taeseokyi/reefkeeper/docs/notes/feedback-one-change-at-a-time.md

# feedback-one-change-at-a-time

> KH 측정 시스템 튜닝/실험은 한 번에 하나씩만 변경하고 효과 측정 후 다음으로

---

아쿠아위즈 KH 측정 시스템의 파라미터·시퀀스 튜닝 시 **한 번에 한 가지만 변경**하고 그 ΔpH/dKH 효과를 측정한 뒤 다음 변경으로 넘어간다. 여러 개를 동시에 바꾸면 어느 요인이 작용했는지 규명 불가.

**Why:** 폭기 30→20분과 대칭화(ref/tank 분리측정)를 동시 적용해 "30 vs 20" 비교가 교란된 전례가 있음 ([project-kh-offset-aeration-test](project-kh-offset-aeration-test.md)).

**How to apply:** 변경 후보가 여러 개여도(폭기시간·헹굼제거·`STABLE_SECS`·`CONV_EPS` 등) 묶지 말고 순차 적용, 각 단계마다 정시 측정(05:00/13:00/21:00)으로 효과를 확인한 뒤 다음으로. 변경 전에는 현 상태를 먼저 관찰(예: 21:00 ΔpH 변동)해 기준선을 잡는다.

**단위는 "변수 개수"가 아니라 "인과 축(메커니즘)" (사용자 정정 2026-06-16):** `STABLE_SECS`(샘플링 전 안정화)와 `CONV_EPS`(수렴 채택문턱)는 **둘 다 "안착·평형된 값만 채택"하는 동일 축**이라 한 묶음으로 동시 변경해도 원칙 위배 아님(같은 가설 검정). 분리 기준은 서로 다른 메커니즘일 때 — 폭기/CO₂(`ron`·`AIR_SECS`) vs 경로/접합(헹굼·KCl) vs 안정성(STABLE·CONV_EPS). **같은 축의 2변수를 "분리 안 됨"이라 경고하지 말 것(과한 경고).**
