taeseokyi/reefkeeper/docs/notes/project-kh-v4-firmware-state.md

# project-kh-v4-firmware-state

> "KH 측정 현재 상태 스냅샷(2026-06-17 말) — V4 평형추종 측정 + 신펌웨어(트림평균) 플래시 완료, dkh.dat 규약, 미해결 핵심=폭기가스 안정화"

---

이번 세션(2026-06-17) 끝 시점의 **현재 상태 + 다음 단계** 스냅샷. 상세 이력은 [project-kh-offset-aeration-test](project-kh-offset-aeration-test.md)와 `docs/measurement-ledger.md`(측정 시각순+코드버전 V0~V4 정의+진단).

**측정 코드 = V4 (`bin/measure_kh_once.py`, Windows `C:\dkh\work`에도 배포):**
- **폭기 중 측정 + 진짜 평형(평탄)까지.** 평탄 판정 = **정수 milli-pH 윈도우 span**: 최근 4개 `round(ph*1000)`의 max−min ≤ **2 mpH**. (float 비교 `abs(d)<=0.001`은 0.001 경계 지터로 못 씀 → 정수 비교. 연속-Δ는 느린 크리프에 조기 latch라 폐기.)
- 2-phase: **[A]** tank·ref 동시폭기 + tank 평탄까지 측정(ref는 홀딩서 co-aeration) → **전이 무대기**(airoff → `m1b:82` 완전배출[오염방지, 단축불가] → `m2f:60`) → **[B]** ref 평탄까지(co-aeration이라 빨리). 간격 30s.
- **무한대기 방지:** `PHASE_MAX_SECS=2400`/phase + `MEAS_MAX=80` + 연속 측정실패 `FAIL_MAX=5` + 시리얼 read 타임아웃. 미평탄 상한 도달 시 마지막값+경고(행 안 함).
- 오류/비정상 종료 시 `_safe_cleanup`(에어OFF+측정챔버 배출+KCl 소크 복원). KCl 소크 완료 미검증이면 에러로 0.0 기록.

**dkh.dat 규약** (`HH ref_pH tank_pH ref_kh(8.448) tank_kh temp`):
- **에러 표식 = 5값 전부 0**(측정실패/타임아웃/KCl소크 실패). ★**에러 래치**: 측정 전 마지막 줄이 에러표식이면 *측정 생략하고 에러표식만 재기록* — 수동으로 마지막 에러줄 삭제 전까지(오류 무인 반복 방지).
- **평탄 미도달 = `tank_kh` 음수(−)** 표식(값 크기 유지). 전부-0 에러표식과 구분돼 래치 안 걸림.
- 서버 `bin/dkh_server.py`는 `float(parts[4])` 그대로 반환 → **음수 그대로 출력**(수정 불요). 0.0=에러.

**진단 도구:** `bin/test_aeration_plateau.py`(tank 단일 평형곡선; V4와 **동일 평탄기준**, 종료 시 finally서 KCl 소크). `bin/plateau_analyze.py`(CSV 오프라인 알고리즘 검증).

**펌웨어 (2026-06-17 ~20:50 플래시·`help` 검증 완료, 보드 라이브):**
- **전위 = 트림 평균**(`TRIM_N=16`: 64샘플 정렬 후 상·하위 16개 버리고 중앙 32개 평균; 버블 스파이크 제거). 차동이라 절대 pH만 미세변동, dKH 무영향.
- **seq / air: / wait: 명령 제거**(미사용·레거시) → flash 98→90%, RAM 83→58%.
- **신규 명령: `roff`/`toff`**(D12 에어/D13 PWM 선택 OFF; ron/ton의 짝), **`stop`**(전체 모터+핀 OFF=motorAllStop+stopAir). help/status 정리(status에 D12/D13 핀상태 표시).
- 플래시 방법: 클론 Nano(CH341)=신 부트로더(`arduino:avr:nano`). **HC-06이 D0/D1 하드웨어 시리얼 공유**라 보드에 꽂은 채론 USB 업로드 충돌→**Nano 빼서 단독 USB 플래시**. 단독 시 ADS1115 없어 `while(1)` 정지(ino) → help 검증은 보드 재장착 후 COM15(블루투스)로.

**★★★밀폐 검증 ①② 모두 성공 = 밀폐 우위 확정 (2026-06-19 05:00+13:00):**
- 밀폐 두 점: `05 7.976 7.968 …8.283 28.1`(ΔpH −0.008) / `13 7.957 7.947 …8.255 28.6`(ΔpH −0.010). 둘 다 tank 4회·125s/ref 6회·203s 평탄(span≤2), 단조·진짜 평탄·경고 없음·빠름.
- **검증① (새벽 dip 소멸) 성공:** 3회 재현되던 −0.043~−0.059 dip이 **−0.008**로 붕괴 = 방 CO₂ 유입 차단. 절대pH ~7.97로 6/17 새벽(7.97, −0.058)과 같은 수준인데 dip만 소멸=깨끗한 대조.
- **검증② (증발 흩어짐↓) 성공:** 새벽→낮 dKH 점프가 **개방 +0.29(6/18 7.657→7.950) → 밀폐 −0.03(8.283→8.255)로 ~10배 축소.** 6/18 +0.29를 만들던 한낮 증발 농축이 밀폐로 사라짐. 두 밀폐 점 타이트 군집(ΔpH −0.008/−0.010, dKH 8.283/8.255). 절대pH도 ~7.97→7.95 거의 불변(개방 0.4 스윙 대비)=헤드스페이스가 5L 버퍼로 핀고정→방CO₂ 일주기서 분리. 공통모드 ~20mpH 동시하강에도 ΔpH 보존=차동 정확.
- **부수효과 = 평탄 폭발적 단축(드리프트 레버 a+b 동시):** 과거 새벽 33회→4회, ~50분→~5분 → tank↔ref gap 붕괴 → 17:08식 inter-phase 드리프트 구조 제거. 28.6℃까지 펌프발열 폭주 없음.
- **원시오차 −0.78→~−0.18(−0.165/−0.193), 영점보정 필요성 약화·급하지 않음:** 무보정으로 이미 ±0.25 안. offset이 작고 안정해 보이나 **n=2·동일물/전극 → 21:00·시계열(또는 신선해수 새 널)로 재확인 후 영점보정 결정**([feedback-validation-independent-replication](feedback-validation-independent-replication.md)).
- **★★★★6/20 06~07시 라이브 검증(환경=05:00 동일·냉방 27.9℃) = net 게이트 성공 + 폐루프 CO₂ 상쇄 실패 발견(밀폐 채택 목적 반증):**
- **net 게이트**(최근4 span≤2mpH **AND** net=|양끝차|≤1mpH) 추가 → tank/ref 플래토 라이브 실행. CSV=`aeration_plateau{,_ref}.csv`, 신규 `bin/test_aeration_plateau_ref.py`.
- **① net 게이트=성공:** tank 7.829↗7.850 단조(기존 span≤2면 @546s 7.849서 멈췄을 것 → net 게이트가 @624s 7.850 net=1까지), ref 7.906↗7.909 즉시 평탄(span0 net0). net=span 단조꼬리 정확히 차단=6/20 가짜 latch 재발 방지 입증. → measure_kh_once.py 적용 검토.
- **② ~~폐루프 CO₂ 상쇄 못 줌~~ → ★결론 철회(부피 오판, 사용자 지적):** 별도 실행 tank 7.850 / ref 7.909(40분 차) 59mpH 갈라짐을 "물이 헤드스페이스 지배"로 본 건 틀림. 실제 부피 재계산(pCO₂ 400µatm당): **30mL 시료 ~3µmol ≪ 4L 헤드스페이스 ~65µmol ≪ 5L 위즈수조 ~500µmol** → 거꾸로 헤드스페이스/5L이 30mL 시료를 지배·핀고정. **닫힌 공간 평형 이뤄지고 CO₂ 상쇄돼야 맞음(사용자 직관 옳음).** 59mpH는 폐루프 실패가 아니라 **두 실행 40분 차의 헤드스페이스 드리프트(수동 핀이 느림)** 또는 널 차이. 동시 co-aeration이면 맞아야 함(6/19 −0.008이 증거).
- **★근본 결함 = 수동 핀이 *느림*(용량 아님).** 5L이 용량상 헤드스페이스를 지배해도 수동 수면확산은 시간 단위라 ~15분 측정 중 못 잡아줌 → 헤드스페이스 드리프트.
- **★★해법 채택(사용자 6/20) = 5L 위즈수조 능동 폭기 앵커.** 홀딩 에어스톤을 5L로 이전 → 5L↔헤드스페이스 능동·빠른 교환 → 헤드스페이스가 수 분 내 5L pCO₂에 단단히 고정 → tank·ref가 Phase A/B 내내 같은 앵커에 평형(시간차 무해). 30mL 수요(3µmol)≪5L 버퍼(500µmol)라 정량 충분. ref=5L 물이라 자동 정합 → ΔpH=순수 알칼리니티. **밀폐 유지(증발통제)+핀 약함/느림만 제거.** ⟹ **V5(ref 무폭기) 철회·V4 복귀(net 게이트 유지)로 정리(아래).**
- **남은 단일 확인 = 널/알칼리니티:** tank 200mL 6일 증발 가능성 → 신선 동일 해수 널로 ΔpH→0 검증. (개방/외기라인은 백업, 5L 앵커가 1순위.) [reference-aquawiz-overseas-cases](reference-aquawiz-overseas-cases.md)
- **★코드 상태(2026-06-20 배포):** `measure_kh_once.py` = **V4 + net 게이트**(span≤2 AND net≤1). V5 ref-무폭기/measure_ref_settled/SETTLE 제거. Phase A 주석=5L 앵커 토폴로지. **Windows `C:\dkh\work` 배포 완료, PORT=COM9**(스케줄러 13:00~ 적용). test_aeration_plateau{,_ref}.py 도 net 게이트 보유. **★하드웨어 완료(사용자 6/20): 에어스톤 홀딩→5L 위즈수조 물리 이전함** → 5L 앵커 셋업 가동. 다음 측정부터 효과 발현 예상.

**★★★★★★★6/20 21:00 = B1 검증 성공 + 물 gap −0.053 확정:** `21 7.979 7.926 …7.474 27.0`(ΔpH −0.053). tank 7.913↗7.926 **25회·945s**, ref 7.977↗7.979 9회·320s, 둘 다 span4=0·net8=1 진짜 평탄. **(1) net8 조기latch 차단 입증:** 10회 `span4:2 net8:5`(span 만족인데 net8>1이라 안 멈춤=20:29이면 latch했을 지점), net8 5→1로 줄며 25회 진짜 평탄(22~25회 전부 7.926). **(2) 20:29 tank ~5mpH 미평형 확정:** B1으로 7.921→**7.926** = 20:29 "10회 반토막"은 조기latch였음. **(3) 물 gap ≈ −0.05 (7번째 확증):** 깨끗한 −0.053(dKH 7.474), tank≈7.926/ref≈7.979 완전평형 → 순수 물 차이(tank 알칼리니티 < ref). **(4) ref도 9회·320s**(net8 최소 8회, 예상된 느려짐). **⚠️ 대가=총 ~21분**(tank 945s long pole). **운영 구성 확정=tank-먼저+5L동시폭기+파킹+B1+밀폐. 결정타=신선 동일 해수 널.**

**★★★★★★6/20 19:50·20:29 = gap 6번째 확증 + 속도 설계 성공 + B1(net 룩백 4→8) 적용:**
- **19:50 (ref-먼저 재현):** `19 7.975 7.926 …7.539 26.9`(ΔpH −0.049). tank 18회/ref 7회. gap 패턴 재현.
- **20:29 (새 흐름=tank-먼저+5L 동시폭기+홀딩 파킹+즉시 ref):** `20 7.977 7.921 …7.426 26.9`(ΔpH −0.056). **(1) 속도 설계 성공:** ref 7.976서 출발(이미 천장)→**4회·125s 역대 최速**(동시폭기 co-aeration 입증), 전이도 파킹(m2b)+ref직접(m4f)로 단축, 총 측정 ~절반(950→485s). **(2) gap −0.056=6번째 확증**(누적 −0.044~−0.056) → 진짜 물 차이 확정적. **(3) ⚠️ tank 10회·360s는 진짜 가속 아니라 조기 latch**(평탄값 7.921=역대 최저, 4점 net=1이 슬로우 꼬리서 10회에 위장)→dKH 7.426(최저)·gap 최대에 기여.
- **★B1 적용(코드):** `FLAT_SPAN_N=4`(흔들림)·`FLAT_NET_N=8`(드리프트 룩백, span보다 길게)·`FLAT_NET_MPH=1`. span=뒤 4개, net=8개 양끝차. 20:29 데이터 검증=8점이면 net=8>1로 10회 latch 차단→진짜 평탄까지. measure_kh_once.py 반영·Windows 배포 완료. (test 스크립트는 아직 4점 그대로.) **★최적 운영 구성 확정=tank-먼저+5L 동시폭기+파킹+net 게이트(B1)+밀폐**; 순서/폭기는 정확도 무관(속도만), 정확도 레버는 이제 *물(신선 널)*뿐.

**★★★★★6/20 18시 통제실험 2점 = 장치 가설 4개 연쇄 기각 → "진짜 ΔKH(널 degrade)" 유력:**
- **18:11 (2배폭기, 구코드 tank-먼저):** `18 7.979 7.924 …7.443 26.4`(ΔpH −0.055). tank 19회·711s, ref 5회·164s. **2배 폭기가 등반시간 15:00 대비 ~절반(1296→711s)으로 줄였으나 ΔpH 안 고침(−0.046→−0.055) ⟹ gap은 kinetics 아님.**
- **18:57 (2배폭기, 신코드 호스스왑/ref-먼저):** `18 7.975 7.931 …7.636 26.7`(ΔpH −0.044). ref 7.972↗7.975 5회·164s, tank 7.908↗7.931 20회·750s, 전 과정 정상 완주. **ref-먼저(웜업)도 gap 못 고침 → 순서 아티팩트 기각.** ΔpH −0.055→−0.044는 tank-먼저 산포 안 변동(무의미), tank 등반도 19→20회로 거의 동일.
- **★★장치 가설 4개 기각:** ①kinetics(2배폭기) ②순서/웜업(ref-먼저) ③측정경로/홀딩(18:11=ref가 홀딩경유 vs 18:57=tank가 홀딩경유인데 **부호 안 뒤집힘=tank가 늘 낮음**) ④미평형(18:57 tank가 head-start로 더 높이 7.908 출발했는데 **같은 7.931 안착**=다른 출발→같은 도착=진짜 평형).
- **⟹ 결론: tank·ref 물의 진짜 차이(널 degrade).** tank가 같은 pCO₂서 ref보다 낮은 pH = **tank 알칼리니티가 더 낮음.** 부호상 증발(농축=KH↑=pH↑)의 반대 = **알칼리니티 손실**(6일 된 200mL 개방 tank의 CaCO₃ 석출/생물막/분기). raw 오차 −0.81이 이 물 차이에서 옴. tank≈7.93/ref≈7.975/gap≈−0.045가 4런 내내 바위처럼 안정.
- **★★★다음 = 신선 동일 해수 널(결정타):** 신선 해수 분취 즉시 측정 → **ΔpH→0이면 옛 tank물 degrade 확정(계측 정상·영점 불요)**, 여전히 −0.045면 계통 잔여(챔버/프로브 비대칭)→영점보정 검토. 코드 상태: measure_kh_once.py = ref-먼저+호스스왑 배관(m4=5L↔측정챔버, m1=본수조↔홀딩, _safe_cleanup도 m2b→m1b로 수정), Windows 배포 완료, net 게이트 4점 유지(B1 미적용).

**★★★★6/20 15:00 = 5L 앵커 첫 실측 = 기대 미달 + net 게이트로 "실제 gap" 확정:** `15 7.975 7.929 …7.602 27.1`(ΔpH **−0.046**, 원시오차 **−0.846**). (자동 14:35 실행은 `m1b:72` **모터1 타임아웃**=튜브 막힘 실패→사용자 튜브 점검 후 15:55 재실행 정상=기계 문제 해결.) **(1) net 게이트 의도대로 작동:** tank 7.868↗7.929 **34회·1296s(21.6분) 끝까지 단조상승**, net 22~33회 3에 묶여 안 멈추다 34회서 span=1·net=1 *진짜* 평탄 latch(05:00 11회 조기latch 의심을 net 게이트가 교정). ref 7.966↗7.975 11회·399s→net=1. **(2) ★핵심 업그레이드: 21분 진짜 평탄까지 갔는데도 ΔpH −0.046 ⟹ 음수 dip은 가짜 조기latch 아티팩트가 아니라 tank·ref 진짜 평형 pH가 46mpH 갈라진 *실제 gap*.** 05:00 "조기latch 탓?" 가설을 net 게이트가 배제 → dip 원인=미평형 아닌 *천장 불일치*. **(3) 유력 원인=순서 아티팩트(앵커 천장 미확립):** 같은 물·헤드스페이스인데 tank(먼저 7.929)<ref(나중 7.975). 앵커(5L 폭기)를 phase A와 *동시에* 켜서 tank 측정 21분 내내 헤드스페이스가 5L pCO₂로 올라가는 중(천장 미완성)→tank 낮은 천장 평형, ref(25분 뒤)는 확립 후라 진짜 천장. tank +61mpH 단조등반이 정합. 냉방 27℃가 τ↑로 악화. **(4) 온도 비원인:** 양 phase 27.1~27.4 안정→측중 dT/dt 작음. **(5) 6/20 두 점(05:00 −0.051·7.521, 15:00 −0.046·7.602) 모두 6/19 좋은군집(8.25~8.42)보다 ~0.7~0.9 낮음=냉방+앵커 후 일관 dip.** **★다음 결정 테스트: 앵커 *예비폭기(warmup)* — phase A 시작 *전* 수 분 5L 폭기로 천장 먼저 박기(예측=tank 등반 급감+ΔpH→0).** net 게이트=코드 성공(실제 gap 노출), 튜브 점검=기계 성공.

**★★★6/20 05:00 = 새벽 dip 재출현(ΔpH −0.051, dKH 7.521) — 밀폐 새벽 검증 1성공+1문제 혼재:** `05 7.922 7.871 …7.521 27.7`. **밀폐 CO₂ 실패로 단정 금지 — tank 미평형 조기 latch 유력.** tank 7.861↗7.871 **11회·399s 11번 연속 단조상승(한 번도 안 꺾임=진짜 평탄 아님)**, ref 7.921↔7.922 4회·125s 흔들림(진짜 평탄). ⟹ tank가 ref(7.922) 향해 등반 중 못 채운 ~50mpH가 가짜 dip으로 latch(plateau_analyze 경고 "느린 지수꼬리 조기 latch", span≤2mpH 약점이 물림). 6/19(tank 출발 7.967=평형근처, 4회)와 차이=이번 tank 출발 7.861(60mpH 아래)→긴 등반. **냉방으로 박스 식음(28.1→27.7℃)→가스교환 τ↑→399s** 정합. **★냉방 후 두 점 다 튐:** 냉방전 6/19 05/13 타이트(−0.008/−0.010)→냉방ON 21:00 +0.166→냉방후 05:00 −0.051, 열정상상태 상실(28→26.8→27.7)이 교란(이번 측정중 T=27.7 안정→측중 dT/dt보다 *냉각 후유증*=tank 출발 산성화+느린 kinetics). **다음 행동: ①온도 안정화 1순위(냉방 끄거나 정상상태 안정 후 재측정) ②평탄기준 보강 검토(최근 윈도우 단조면 latch 금지=꺾임 요구) ③깨끗한 새벽 재현 필요(밀폐 우위 결론은 6/19 1점이라 잠정).**

**★★21:00 검증 완료(6/19) = offset "완벽 상수 아님, 단 흩어짐 작아 무관" 확정:** `21 7.969 7.968 …8.421 26.8`(ΔpH **−0.001**=측정 분해능 1mpH 한계=사실상 완벽한 널, 원시오차 **−0.027** 역대 최소). tank 7.970↘7.968/ref 7.968↗7.969 둘 다 4회·125s 평탄·경고없음·빠름(핀고정 유지). **밀폐 3점 시계열: ΔpH −0.008/−0.010/−0.001, dKH 8.283/8.255/8.421.** 05:00↔13:00 타이트(Δ0.028)했으나 **21:00이 +0.166 위로 점프 → "−0.18 안정 상수" 가설 반증**(offset 변동 ±~0.085 dKH). **그러나 세 점 무보정 원시오차 −0.027~−0.193 전부 ±0.25 안**(평균 −0.128, SD~0.073). ⟹ **정밀 영점상수 박기 부적절(상수 아님)·무보정으로 목표 충족 → 영점보정 사실상 불요**([project-accuracy-target](project-accuracy-target.md) 완화기준 충족). 절대pH 7.95→7.969 거의 불변=핀고정 지속. **★confound=냉방 과도(사용자 확인): 28.6→26.8℃(−1.8℃)는 펌프안정 아닌 *냉방기 가동* 외부개입.** dKH +0.166과 타이밍 일치 ⟹ 인과 후보. 메커니즘=드리프트 구조 온도판 **오차 ≈ gap(tank↔ref 시간차) × dT/dt**(냉방 ON 직후 온도 능동하강 중 tank/ref ~125s 차로 다른 온도 측정→정적온도는 차동상쇄·과도는 gap만큼 누출). ⟹ 밀폐 우위 안 깸, "측정 중 환경(CO₂·온도) 안정 필요" 원칙 온도축 재확인. **offset 변동=랜덤 전극드리프트 아닌 통제가능 열과도 신호**(온도 안정 시간대 측정 시 소멸 예상). 검정=냉방 정상상태(온도 안정) 후 재측정.

**★★(이전) V4 개방 결론 (2026-06-18 13:00 — 3번째 점이 baseline 상수성 반증):**
- **V4 완전평형이 방 CO₂ 의존성을 제거했다(입증·강화됨).** V4 완전평형 점 3개: 6/17 21:00(저CO₂,절대8.1) **−0.042** / 6/18 05:00(고CO₂,절대7.7) **−0.043** / 6/18 13:00(저CO₂,절대8.1) **−0.026**. 절대pH 7.7~8.1 세 점이 CO₂를 안 따라감 → 의존성 제거 결론 오히려 강화. 곡선 전부 단조·진짜 평탄 latch(span2). 새벽 05:00 tank는 **하강**(7.960↘7.695, 방CO₂ 천장이 출발pH보다 아래)인데도 차동이 공통모드 상쇄. 과거 새벽 −0.058/−0.059 → −0.043 개선.
- **기존 "새벽 −0.058 문제"는 레벨 효과였고 V4가 해결.** 불완전 평형 + 200mL(빠른)/5L(느린lag) 비대칭으로 한쪽만 고-CO₂ 천장 도달한 산물. 완전평형이 양쪽 같은 천장 안착.
- **★baseline은 상수가 아님(13:00이 실측 확인) → 영점보정 보류 유지.** 6/17~18 두 점(−0.042/−0.043)은 같은 물·증발·전극에서 CO₂만 바꾼 통제(=n=1, 독립표본 아님). **6/18 13:00이 같은 저CO₂에서 −0.026으로 돌아오며 "−0.042=이전가능한 장치 상수" 가설 반증**(tank_dKH 7.67/7.66→**7.95, +0.29**). 깨끗한 완전평형 3점인데 16mpH 흩어짐 → 장치 구조 오프셋이 아니라 물/증발/전극 드리프트 성분이 큼. 지금 영점보정하면 망침.
- **confound = 증발:** tank 외기개방 200mL 5일째 → 한낮 증발 최대로 KH 실제 농축(ΔKH=0 전제 깨짐, ΔpH +방향=덜음수로 밀림). 단 21:00→05:00 불변·05:00→13:00 계단점프라 증발/전극드리프트/측정변동 미구분. ⟹ **동일 해수 새 널테스트(사용자 진행 예정)가 통제.** 판정: 새 널 독립재현+시계열 타이트 군집(낮SD·무추세·무CO₂상관)이어야 상수 확정→영점 정당, 흩어지면 보류. 그 전 보정값 펌웨어/서버 미적용(서버 값 그대로 통과 유지).
- **스크러버(폭기 가스 안정화) 우선순위 ↓.** CO₂ *레벨*은 V4가 해결. 측정 중 *드리프트*(17:08 비단조 산모양) 케이스에만 필요 — 깨끗한 측정들은 CO₂ 안정이라 V4 단독 완벽.
- **드리프트 오차 ≈ gap(tank↔ref 시간차)×dC/dt → 두 레버:** (a) 가스 기준 고정, (b) **토출량 Q_gas↑로 τ 단축→측정시간·gap 비례 축소**(싸고 소모품 없음=드리프트 보험, 단 offset/증발/평형값엔 무영향·CO₂안정 측정엔 값 동일, 한계=kLa 포화·미세기포 노이즈). 검증=`test_aeration_plateau.py` 세기↑.
- **★레버(a) 채택 = 밀폐(공통 헤드스페이스), 외기라인은 백업 (사용자 결정 6/18).** 차동 요구=절대 pCO₂ 아닌 *공통* pCO₂(알칼리니티 보존). 밀폐=ref·tank가 **한 박스 공기 공유**+외부차단→공통가스 본질 보장. **★보너스: 증발도 잡아 13:00 +0.29 confound 동시 해결**(외기라인엔 없음)=새벽CO₂+증발 두 잔여원 한번에. **★필수: ref·tank가 *하나의 공통* 밀폐 헤드스페이스 공유**(분리 밀폐는 상쇄 깨짐), 펌프 흡입 폐루프. 리스크=박스 느린 드리프트(단 5L 알칼리니티 버퍼가 헤드스페이스 핀고정)·펌프열. reef2reef 밀폐통 성공=현장검증. 검증=밀폐 후 새벽 사이클 1회(dip 소멸+증발 흩어짐↓). [reference-aquawiz-overseas-cases](reference-aquawiz-overseas-cases.md)

**(이력) 17:08 드리프트 실패:** V4 ΔpH −0.063, tank 비단조(8.011→정점8.077→하락8.043, 측정 31분 중 평형 이동), ref(~25분 뒤) 다른 CO₂서 latch=inter-phase 드리프트. ⟹ 완전평형(긴 측정) vs 간격최소(짧은)가 단일프로브+드리프트서 상충. 문 개폐 아닌 *측정 시간대 CO₂ 안정성*이 가름.

**평형 물리(실측):** 완전평형 ~24분, 단 시작격차 의존 로그(17.5~24분). 평형 *값*=방CO₂ 의존, *시간*=시작격차 의존. "완전 폭기=pH 불변" 입증(대기평형이 천장).

**셋업 (확정):** tank=별도 **200mL 외부챔버 외기 개방**(수조 시뮬레이터, 라이브 리프 아님), ref=**5L 김치통**(반밀폐). 둘 다 6/14 20:12 같은물 분취 **널테스트**(진짜 ΔKH=0). 측정챔버는 통에 잠겨 한 펌프(방공기) 폭기. **ron=에어(D12)·ton=PWM(D13) 독립, airoff=둘 다 OFF**(펌웨어 ino). ★규칙: **액체 이동(mXf/mXb) 직전 반드시 airoff.** 프로브 2점보정(calph) 미실시지만 차동이 보정오차 상쇄(slope만 ΔpH 비율, baseline 영점보정).

**다음 단계 (2026-06-20 18시 통제실험 후 갱신, 우선순위순):**
1. **★★★신선 동일 해수 널 = 결정타(1순위).** 18시 2점이 장치 가설 4개(kinetics/순서/경로/미평형) 전부 기각 → 남은 건 진짜 ΔKH 여부. 신선 분취 즉시 측정: **ΔpH→0이면 옛 tank물 degrade 확정(계측 정상)**, 여전히 −0.045면 계통 잔여→영점 검토. [feedback-validation-independent-replication](feedback-validation-independent-replication.md)
2. **(보류) 예비폭기/순서 레버는 폐기** — ref-먼저(18:57)가 gap 못 고쳐 순서 아티팩트 가설 기각됨. 더 안 매달림.
3. **영점보정** — 신선 널 결과 대기. 옛물 degrade면 불요, 계통 잔여면 그때 검토. [project-accuracy-target](project-accuracy-target.md)

**문서 상태 (2026-06-19 갱신):** repo 문서 전부 현재 펌웨어(트림평균·seq/wait/air 제거·roff/toff/stop)+V4 측정으로 현행화. **★밀폐를 "필수"로 문서·그림 전반 반영(사용자 6/19):** 최종 밀폐 폐루프 사진(`docs/images/Sealed_Closed_Loop_Aqua_Whiz_Final_Product.jpg`)을 README·system-setup 헤드라인에 삽입, 위즈탱크 섹션을 "밀폐 공통 헤드스페이스—선택 아닌 필수"로 재작성(분리밀폐 금지 명시+6/19 검증), 설계배경·널테스트현황·운용메모·user-manual 원리 갱신. **다이어그램 2개(system-setup.svg/setup-demo.svg)에 밀폐 공통 헤드스페이스 경계+뚜껑+콜아웃 추가** 및 폐기된 솔레노이드/`seq:air:`/`탈기30분` 표기를 현행(ron 동시폭기·평탄까지)으로 수정. cairosvg 렌더 검증 완료. 이전 동기:  **측정 대장(docs/measurement-ledger.md)**=신뢰성 1차 기록(V0~V4 측정·환경통제·ΔpH 검증·참조 문헌 Fleger2025/Takahashi/Johnson1982 등), 전 문서에 상호 연결. bin↔Windows 동기·Windows 실행은 `C:\dkh\work\` 경로.

**★2026-06-22 calref(ref dKH 역산) 기능 추가 + 실전 투입 가능 + 정리:** `measure_kh_once.py`에 `--setref <수조실측dKH>` 추가 — 인자 없으면 기존 calkh, 있으면 calref(알려진 수조 dKH로 *참조수* dKH 역산·EEPROM 자동저장, dkh.dat 미기록). 펌웨어 `calcRefDKH`가 `refDKH=newRefDKH`+`EEPROM.put` 자동(추가 setref 불요, .ino line 423-424). 절차=setref(측정전 선전송·범위검증)→tank/ref 측정(calkh와 동일)→calref. **mock 시리얼(프로덕션 .ino 응답 모사) end-to-end 검증 19/19 PASS**(measure 시퀀스 calkh==calref·setref·cal만 차이, 새refDKH=knownTank·10^(-(tankPH-refPH))=calkh의 정확한 역산). 배포본==저장소 동기·git origin 동기(7505db2). **함께 제거: `measure_kh_loop.py`(미사용), `firmware/test/` 구버전 시뮬레이터(calckh/seq 잔존·calref 없음=현 펌웨어 불일치), `C:\dkh\work` 진단 부산물(csv/log)정리.** 문서 `system-setup.md` 흐름도 V4 재작성+상한 최신화. 상세 [project-measure-kh-script](project-measure-kh-script.md). **★★운영 경고: 6/22 05:00 측정이 스케줄러 `ExecutionTimeLimit` 55분 초과로 강제종료(dkh.dat 미기록)됨 — PHASE_MAX 7200×2phase=총4h이므로 `ExecutionTimeLimit`는 ≥4h(문서=270분/PT4H30M, 사용자 적용=PT5H)여야 함. 권한상승 PowerShell로 적용·배터리설정 보존.** **★★6/22 22:00 셋업 변경: 외부 챔버를 *마개 있는 대용량 용기*로 교체(기존 ~100mL→대용량, 밀폐 개선·500ml 수용)+완전 널 시료 신선화(참조수 5L에 초기분취 해수 +700ml, 새 외부챔버 소량교체+500ml)→6/22 노화 드리프트 해소. 이후 측정은 이 셋업 기준(첫 측정 6/23 05:00 dKH 8.427). "100mL 외부챔버"는 6/22 21:00까지에만 유효.** **★★6/23 HC-06 블루투스 RF 순단 대응 추가: COM9=인텔 내장 BT SPP가 간헐 순단(보낼 때 이미 끊김)→measure_kh_once.py send() 4계층(연결확인→재연결→재시도3→모터정지 mNs)+keepalive, 소켓 시뮬레이터 회귀테스트(12시나리오/58검증) 신설. 상세 [project-bt-rf-reconnect](project-bt-rf-reconnect.md) [feedback-regression-test-simulator](feedback-regression-test-simulator.md).**
