taeseokyi/reefkeeper/docs/images/dkh_trend_mobile.png

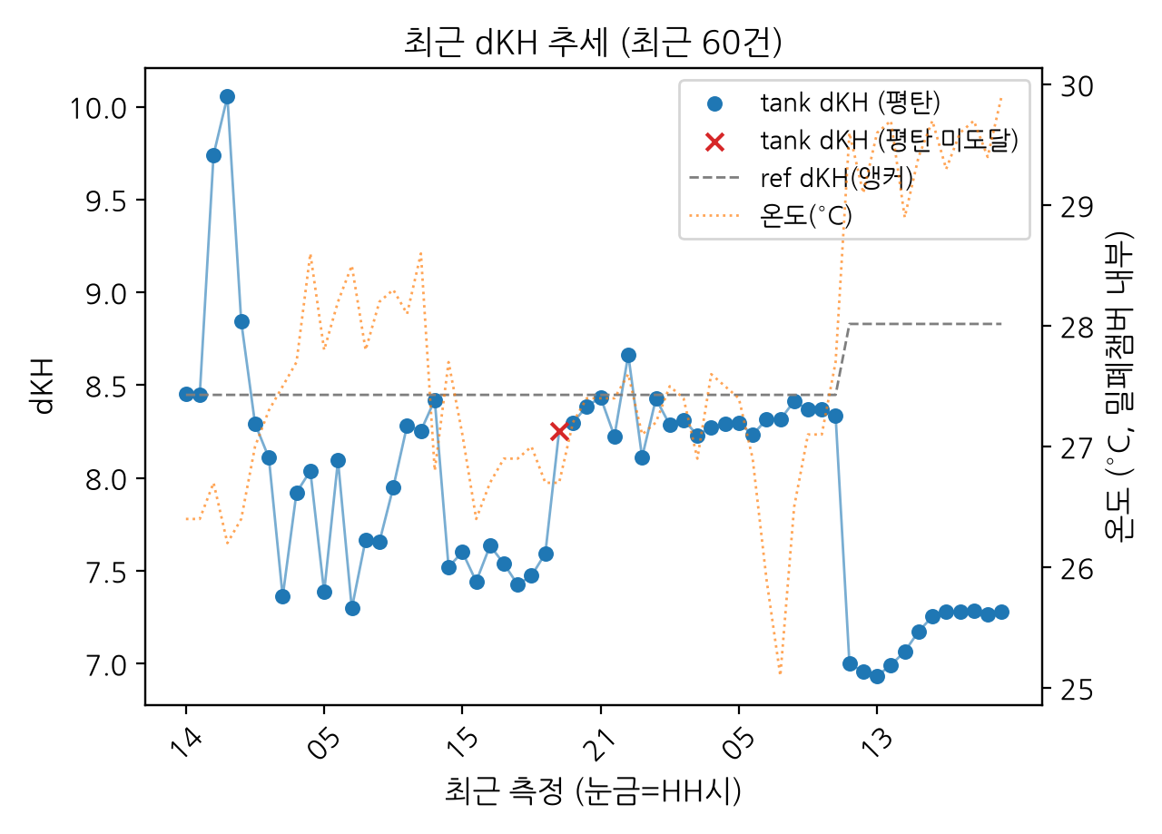
docs/images/dkh_trend_mobile.png
