taeseokyi/reefkeeper/bin/sync_dkh_dat.py

#!/usr/bin/env python3
"""Windows 원본 dkh.dat·measure_kh.log 을 저장소로 동기화하고 GitHub 에 push한다.

cron으로 하루 3회, 측정 스케줄(05/13/21시) + 1시간30분 뒤에 실행(30 6,14,22 * * *)
— 측정이 보통 1시간30분 안에 끝나서 이 시점이면 완료돼 있음. 변경이 없으면 아무것도
커밋하지 않는다(내용이 같으면 push만 시도 — 이전 실행이 네트워크 문제로 push 실패했을
때 재시도 역할). ※측정이 드물게 1시간30분을 넘기면 그 회차는 부분 데이터로 남고, 다음
측정 회차가 되어야 갈아치워짐(하루 3회 고정이라 그 안에서 재시도는 없음).
dkh.dat 그래프(PNG) 렌더링은 여기서 하지 않는다 — push되면 GitHub Actions(plot-dkh.yml)가
data/dkh.dat 변경을 감지해 그린다. measure_kh.log(마지막 측정의 평탄 추종 곡선)는 원본이
Windows에만 있어 Actions가 못 보므로, 여기서 파싱까지 끝내 docs/dkh_plateau.json으로
바로 커밋한다(이 산출물은 추가 렌더링이 필요 없어 Actions를 거칠 이유가 없음).
"""
import fcntl
import json
import logging
import os
import subprocess
import sys

import parse_plateau_log

REPO_DIR = os.path.dirname(os.path.dirname(os.path.abspath(__file__)))
DAT_SRC = "/mnt/c/dkh/work/dkh.dat"
DAT_DST = os.path.join(REPO_DIR, "data", "dkh.dat")
PLATEAU_SRC = "/mnt/c/dkh/measure_kh.log"
PLATEAU_DST = os.path.join(REPO_DIR, "docs", "dkh_plateau.json")
LOCK_FILE = "/tmp/dkh_sync.lock"
LOG_FILE = os.path.expanduser("~/dkh_sync.log")

logging.basicConfig(
    filename=LOG_FILE,
    level=logging.INFO,
    format="%(asctime)s %(levelname)s %(message)s",
)
log = logging.getLogger(__name__)


def run_git(*args):
    return subprocess.run(
        ["git", "-C", REPO_DIR, *args],
        capture_output=True, text=True,
    )


def sync_dat():
    if not os.path.exists(DAT_SRC):
        log.warning("원본 없음: %s (Windows 드라이브 마운트 확인 필요)", DAT_SRC)
        return False
    with open(DAT_SRC, "rb") as f:
        src_bytes = f.read()
    if os.path.exists(DAT_DST) and open(DAT_DST, "rb").read() == src_bytes:
        return False
    os.makedirs(os.path.dirname(DAT_DST), exist_ok=True)
    with open(DAT_DST, "wb") as f:
        f.write(src_bytes)
    return True


def sync_plateau():
    if not os.path.exists(PLATEAU_SRC):
        log.warning("원본 없음: %s", PLATEAU_SRC)
        return False
    with open(PLATEAU_SRC, encoding="utf-8", errors="replace") as f:
        text = f.read()
    result = parse_plateau_log.parse_last_run(text)
    if not result or not (result["tank"] or result["ref"]):
        return False

    prev = None
    if os.path.exists(PLATEAU_DST):
        try:
            with open(PLATEAU_DST) as f:
                prev = json.load(f)
        except (OSError, ValueError):
            prev = None
    if result == prev:
        return False

    os.makedirs(os.path.dirname(PLATEAU_DST), exist_ok=True)
    with open(PLATEAU_DST, "w") as f:
        json.dump(result, f, ensure_ascii=False)
    return True


def sync_with_remote():
    """GitHub Actions(plot-dkh.yml)가 렌더링 결과를 origin에 직접 push하므로,
    이 로컬 저장소를 먼저 최신으로 맞추지 않으면 다음 로컬 커밋이 origin과
    갈라져 이후 push가 전부 실패한다(2026-07-01 밤 실제 발생, 약 7시간 방치).
    건드리는 파일이 서로 겹치지 않아(로컬=data/dkh.dat·dkh_plateau.json,
    Actions=images/*·dkh_latest.json·dkh_series.json) rebase 충돌은 나지 않는 게 정상."""
    fetch = run_git("fetch", "origin", "master")
    if fetch.returncode != 0:
        log.warning("fetch 실패(네트워크?): %s", fetch.stderr.strip())
        return False
    rebase = run_git("rebase", "origin/master")
    if rebase.returncode != 0:
        log.error("rebase 실패, 수동 확인 필요: %s", rebase.stderr.strip())
        run_git("rebase", "--abort")
        return False
    return True


def main():
    if not sync_with_remote():
        return  # 이번 사이클은 포기 — 로컬 상태는 안전하게 보존, 다음 사이클에 재시도

    changed_dat = sync_dat()
    changed_plateau = sync_plateau()

    paths = []
    if changed_dat:
        paths.append("data/dkh.dat")
    if changed_plateau:
        paths.append("docs/dkh_plateau.json")

    if paths:
        run_git("add", *paths)
        commit = run_git("commit", "-m", f"data: 측정 동기화 (자동, {', '.join(paths)})")
        if commit.returncode == 0:
            log.info("커밋됨: %s", commit.stdout.strip().splitlines()[0] if commit.stdout else "")
        else:
            log.warning("커밋 실패/변경없음: %s", commit.stderr.strip())

    push = run_git("push")
    if push.returncode == 0:
        if paths:
            log.info("push 완료")
    else:
        log.error("push 실패: %s", push.stderr.strip())


if __name__ == "__main__":
    lock_fd = open(LOCK_FILE, "w")
    try:
        fcntl.flock(lock_fd, fcntl.LOCK_EX | fcntl.LOCK_NB)
    except BlockingIOError:
        sys.exit(0)  # 이전 실행이 아직 진행 중 — 조용히 종료
    try:
        main()
    except Exception:
        log.exception("동기화 중 예외")
