taeseokyi/reefkeeper/docs/images/펌프-Ph수조파트.jpg

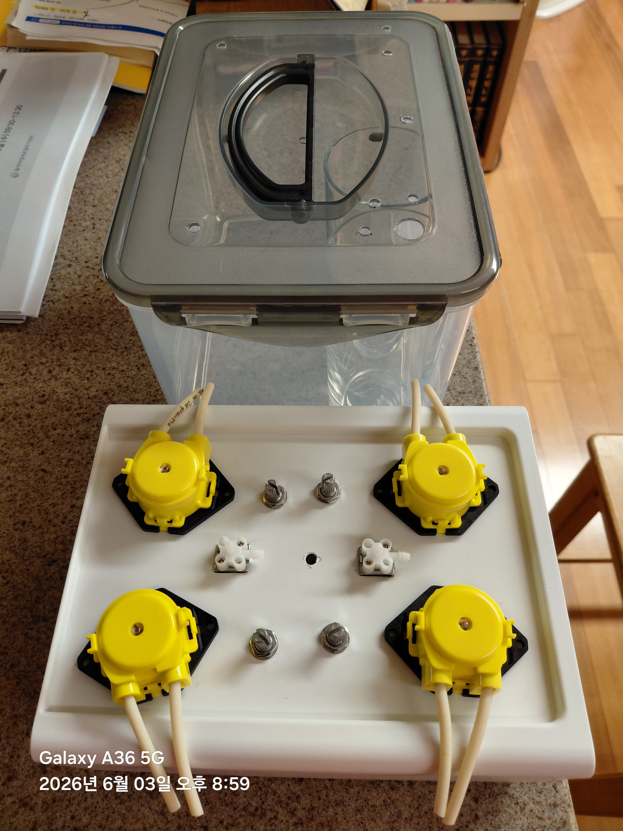
docs/images/펌프-Ph수조파트.jpg
